xyzmataphor/5-Band-Audio-Equalizer/5_Band_Simulation.asc

C1: cap; 64nf
C2: cap; 32nf
C3: cap; 16nf
C4: cap; 8nf
C5: cap; 26.5nf
C6: cap; 13.3nf
C7: cap; 16nf
C8: cap; 8nf
C9: cap; 4nf
C10: cap; 2nf
R1: res; 20k
R2: res; 10k
R3: res; 20k
R4: res; 10k
R5: res; 200k
R6: res; 100k
R7: res; 5k
R8: res; 2.5k
R9: res; 5k
R10: res; 2.5k
R13: res; 3.5k
U1: LT1022
U2: LT1022
U3: LT1022
U4: LT1022
U5: LT1022
U6: LT1022
U7: pot
U8: LT1022
U9: pot
U10: LT1022
U11: pot
U13: pot
U15: pot
V1: voltage; 15
V2: voltage; 15
V3: voltage; ""; AC 1
Named nets: 0, np, nn
.ac oct 100 10 30k
SUB_BASS
BASS
MIDS
PRESENSE
TREBLE
.subckt pot 1 2 3
.param w=limit(wiper, 0.001, 0.999)
R1 1 2 {Rtot*(1-w)}
R2 2 3 {Rtot*w}
.ends
INPUT
OUTPUT
OUTPUT BUFFER
SUMMING STAGE
INTPUT BUFFER
